petrbrouzda/VictronRemoteDisplay/VictronDisplay35/src/extgfx/BasicColors.h

#ifndef __BASICCOLORS__H_
#define __BASICCOLORS__H_

// zakladni barvy - Adafruit_GFX pracuje s 16bit barvami 5-6-5
#define	EG_BLACK   0x0000
#define	EG_BLUE    0x001F
#define	EG_RED     0xF800
#define	EG_LIGHT_RED     0xFAEB
#define	EG_GREEN   0x07E0
#define EG_CYAN    0x07FF
#define EG_MAGENTA 0xF81F
#define EG_YELLOW  0xFFE0
#define EG_WHITE   0xFFFF

#endif
